wmi-0/wiihdmi/pictures/PCB.jpg

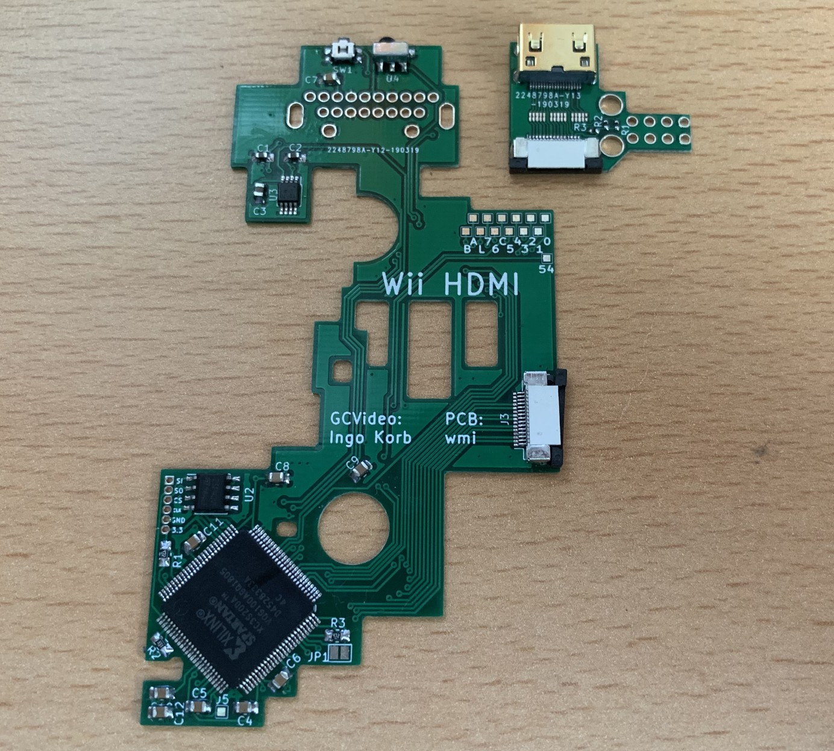
pictures/PCB.jpg
